oystebje/FINGER-FORCE-FEEDBACK/2_Prototype_for_haptic_rendering/CAD/3D-PRINT/CONCEPT2_HANDLE.stl

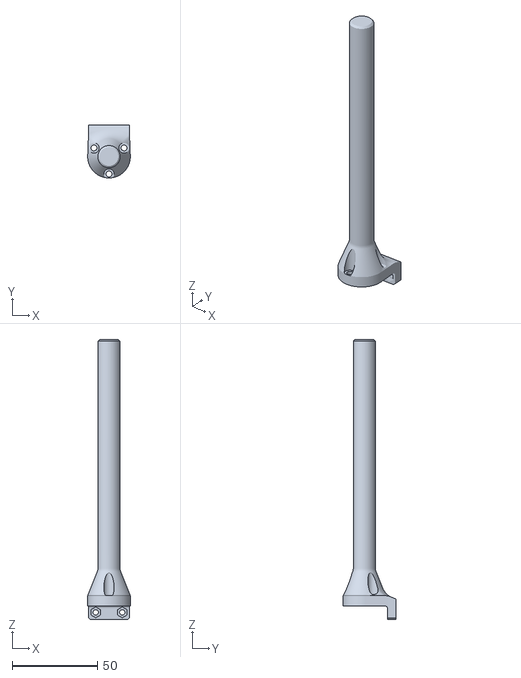
[picture p16: CAD file, 2021-09-15]
2_Prototype_for_haptic_rendering/CAD/3D-PRINT/CONCEPT2_HANDLE.stl
25.0 x 31.0 x 164.0
