oystebje/FINGER-FORCE-FEEDBACK/1_Prototype_for_data_collection/CAD/3D-print/POTMETER_FRAME_3.stl

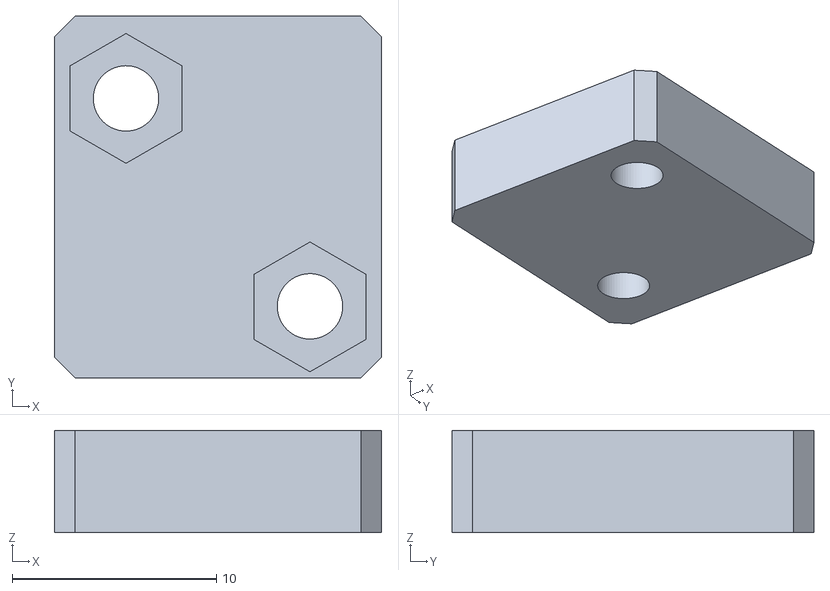
[picture p17: CAD file, 2021-09-15]
1_Prototype_for_data_collection/CAD/3D-print/POTMETER_FRAME_3.stl
16.0 x 17.7 x 5.00
