oystebje/FINGER-FORCE-FEEDBACK/2_Prototype_for_haptic_rendering/CAD/3D-PRINT/TOOL_ADAPTER.stl

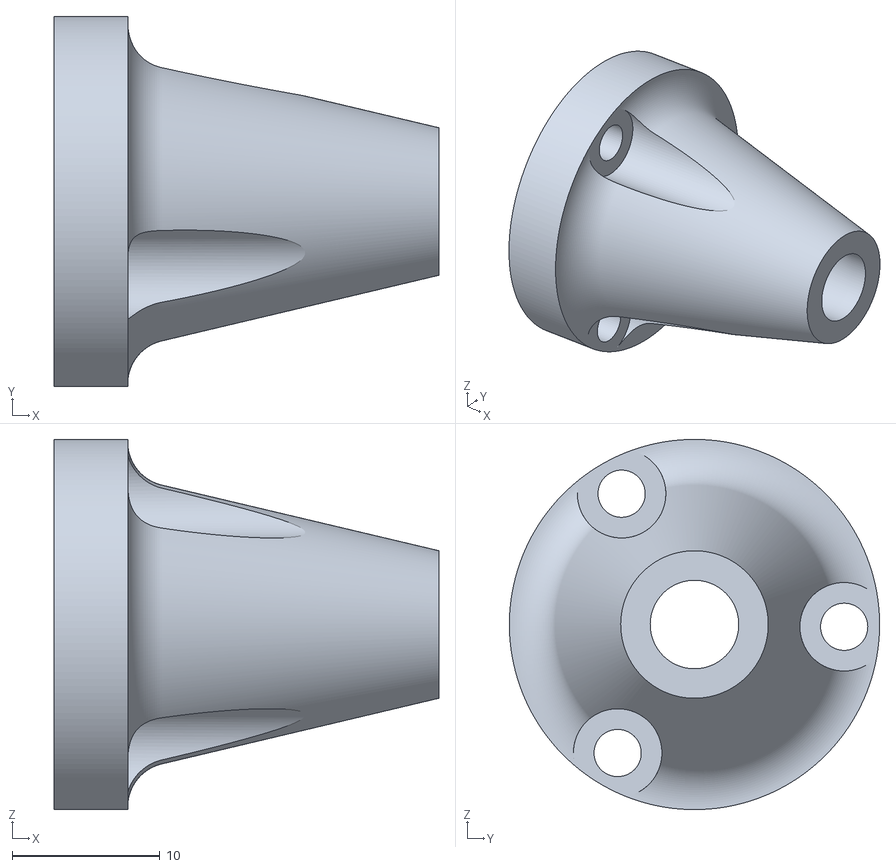
[picture p18: CAD file, 2021-09-15]
2_Prototype_for_haptic_rendering/CAD/3D-PRINT/TOOL_ADAPTER.stl
26.1 x 25.1 x 25.1
