oystebje/FINGER-FORCE-FEEDBACK/1_Prototype_for_data_collection/CAD/3D-print/FSR_TOP.stl

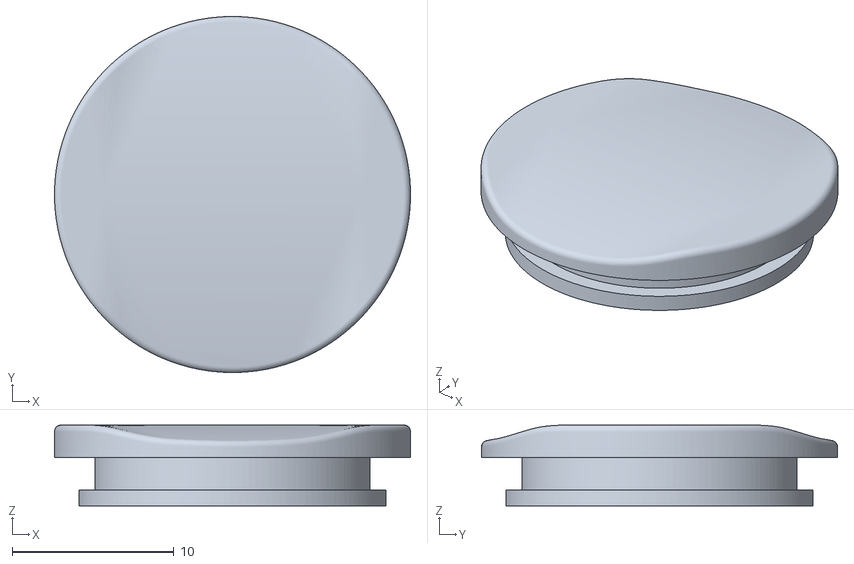
[picture p19: CAD file, 2021-09-15]
1_Prototype_for_data_collection/CAD/3D-print/FSR_TOP.stl
22.0 x 22.0 x 5.00
