oystebje/FINGER-FORCE-FEEDBACK/2_Prototype_for_haptic_rendering/CAD/3D-PRINT/5mm_ADAPTER.stl

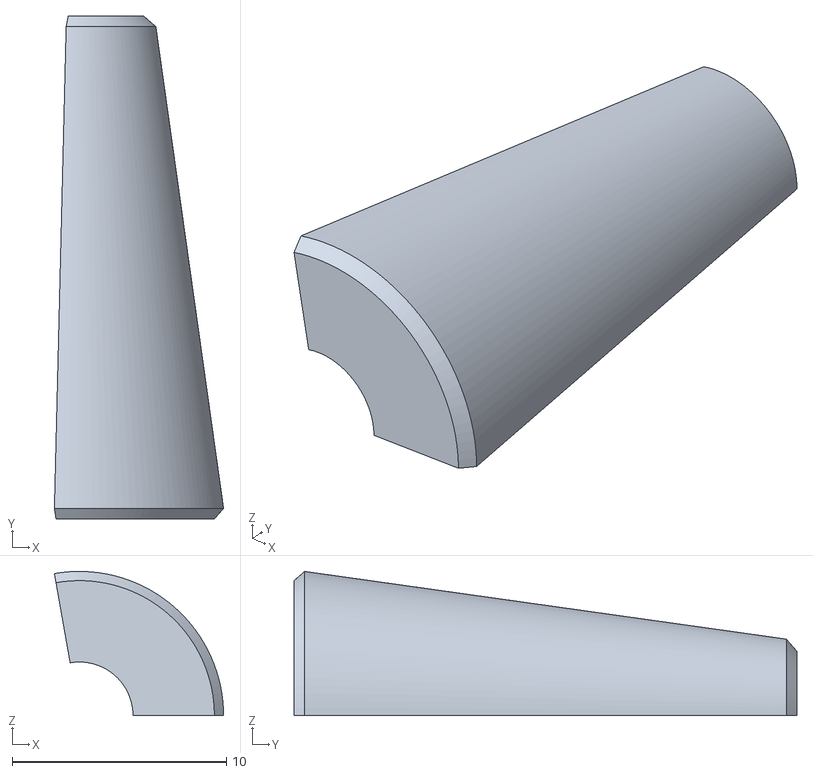
[picture p20: CAD file, 2021-09-15]
2_Prototype_for_haptic_rendering/CAD/3D-PRINT/5mm_ADAPTER.stl
7.90 x 23.5 x 6.73
