oystebje/FINGER-FORCE-FEEDBACK/1_Prototype_for_data_collection/CAD/3D-print/POTMETER_FRAME_2.stl

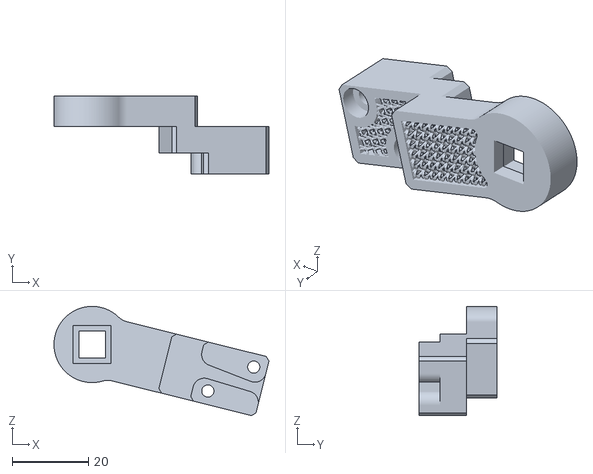
[picture p21: CAD file, 2021-09-15]
1_Prototype_for_data_collection/CAD/3D-print/POTMETER_FRAME_2.stl
56.4 x 20.4 x 28.7
