oystebje/FINGER-FORCE-FEEDBACK/2_Prototype_for_haptic_rendering/CAD/3D-PRINT/FINGER_HANDLE.stl

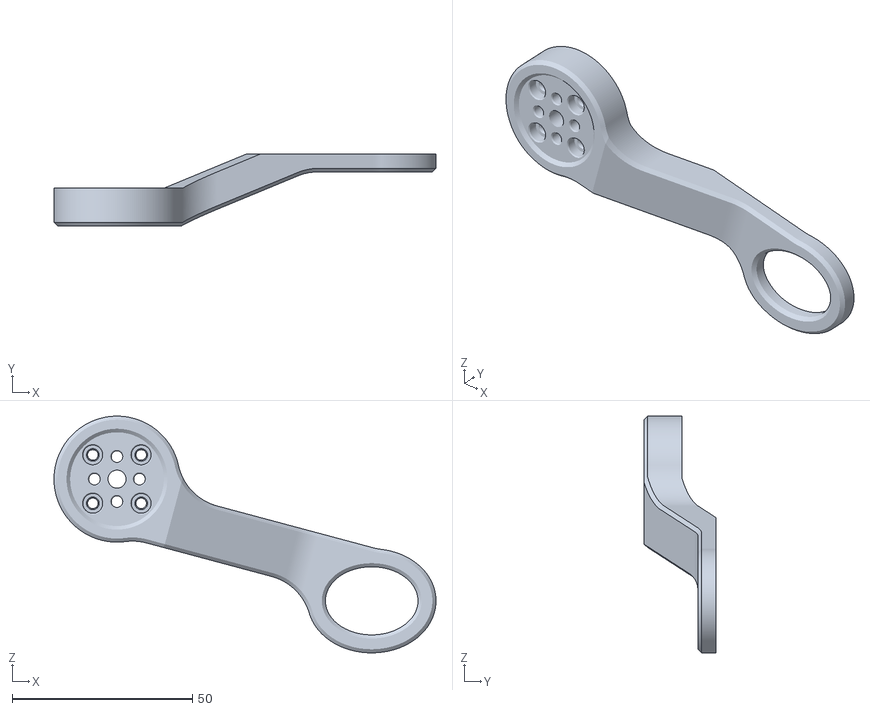
[picture p22: CAD file, 2021-09-15]
2_Prototype_for_haptic_rendering/CAD/3D-PRINT/FINGER_HANDLE.stl
106.1 x 20.0 x 65.7
