oystebje/FINGER-FORCE-FEEDBACK/1_Prototype_for_data_collection/CAD/3D-print/FSR_BASE_RevA.stl

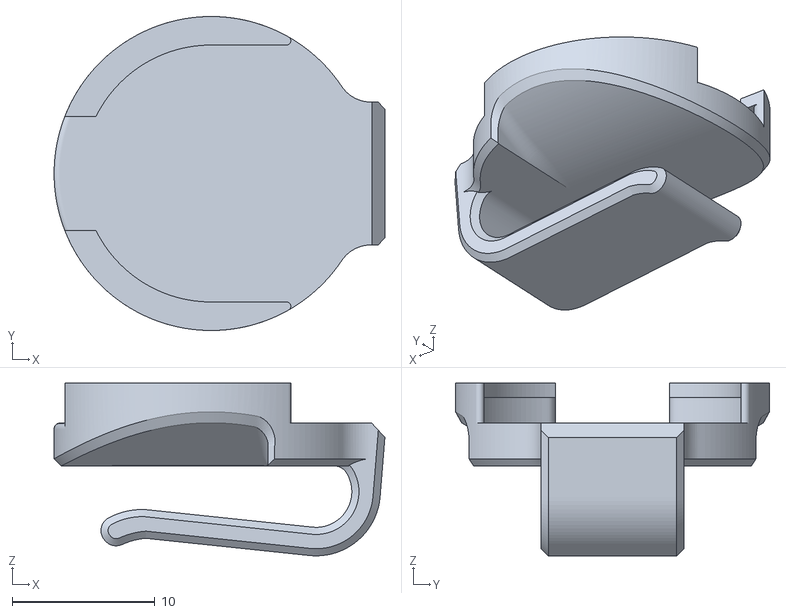
[picture p23: CAD file, 2021-09-15]
1_Prototype_for_data_collection/CAD/3D-print/FSR_BASE_RevA.stl
23.2 x 22.0 x 12.1
