oystebje/FINGER-FORCE-FEEDBACK/1_Prototype_for_data_collection/CAD/3D-print/POTMETER_FRAME_1.stl

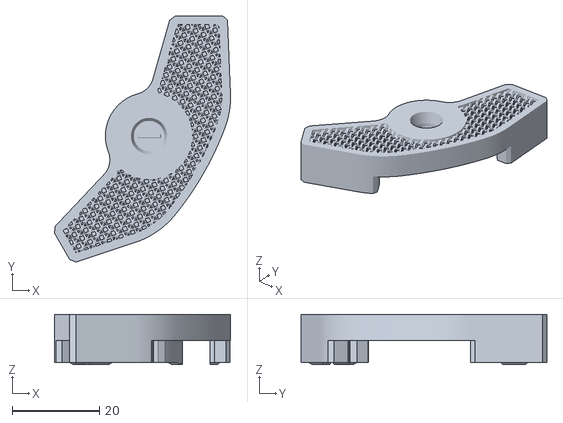
[picture p24: CAD file, 2021-09-15]
1_Prototype_for_data_collection/CAD/3D-print/POTMETER_FRAME_1.stl
40.3 x 56.4 x 11.6
