oystebje/FINGER-FORCE-FEEDBACK/2_Prototype_for_haptic_rendering/CAD/3D-PRINT/THUMB_HANDLE_REVD.stl

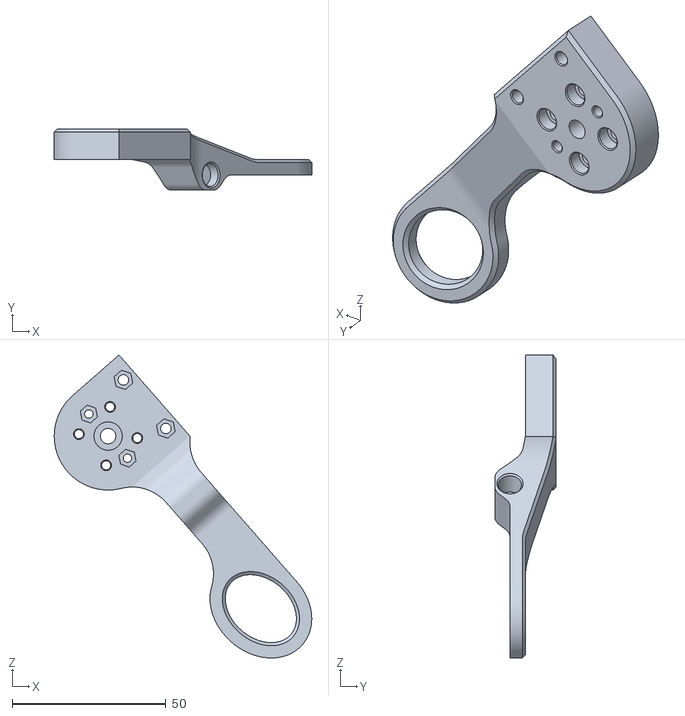
[picture p25: CAD file, 2021-09-15]
2_Prototype_for_haptic_rendering/CAD/3D-PRINT/THUMB_HANDLE_REVD.stl
83.6 x 19.9 x 98.4
